brianz123/sailingStartTimer/CAD_Files/timerBox V4.STL

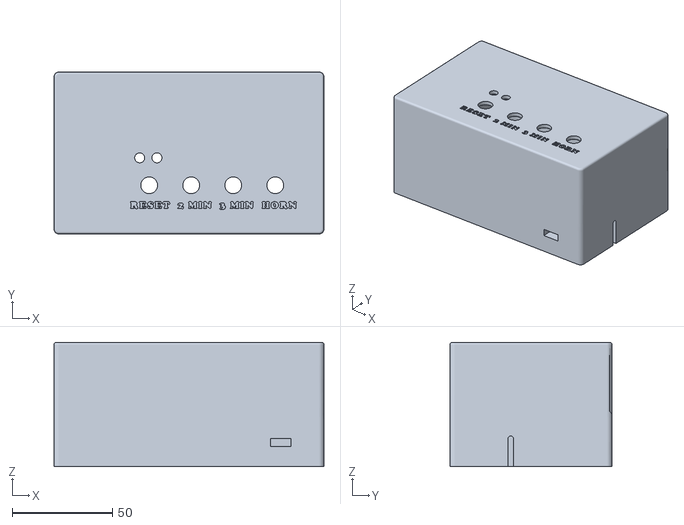
[picture p20: CAD file, 2024-07-31]
CAD_Files/timerBox V4.STL
135.0 x 81.0 x 62.2
